AlexJMcIntyre/TildagonAfterlife/PCB/TildagonAfterlife.kicad_sch

## KiCad design PCB/TildagonAfterlife.kicad_sch (2026-07-25)

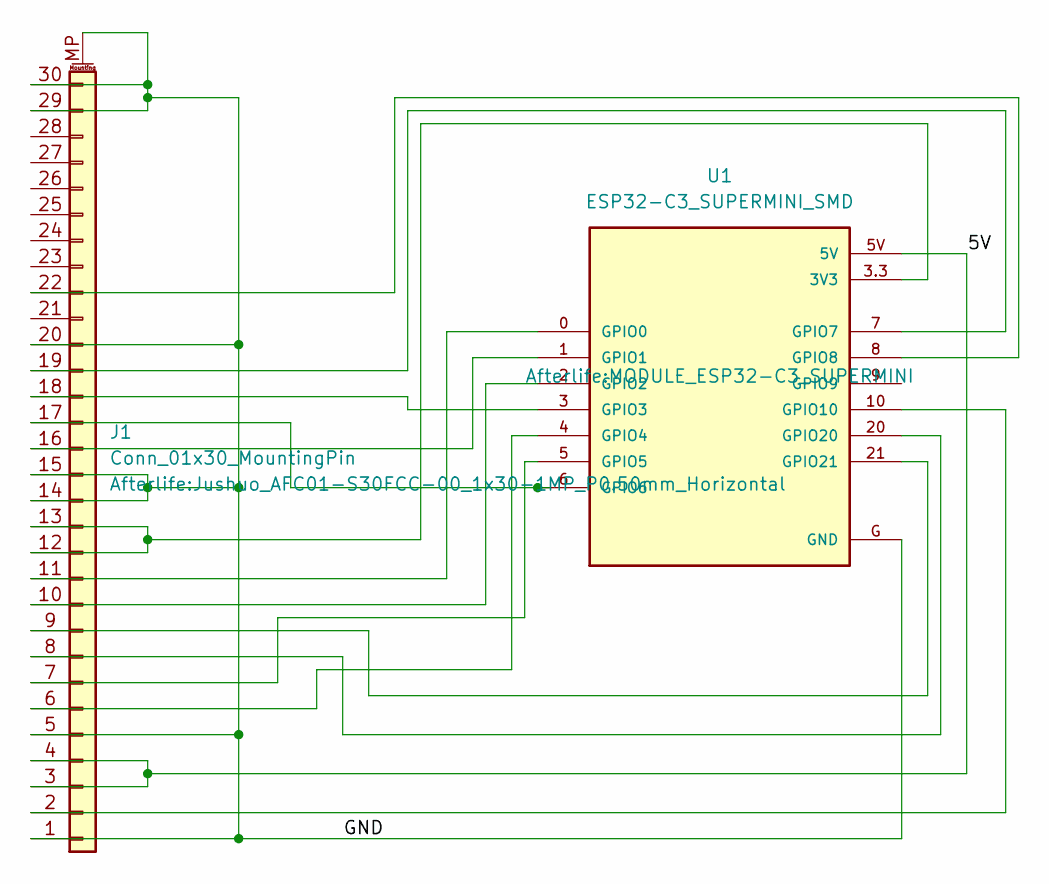
[picture p3: schematic TildagonAfterlife.kicad_sch]

Parts:
J1: Conn_01x30_MountingPin; Jushuo_AFC01-S30FCC-00_1x30-1MP_P0.50mm_Horizontal
U1: ESP32-C3_SUPERMINI_SMD; MODULE_ESP32-C3_SUPERMINI

Connections:
5V: J1.3, J1.4, U1.5V
GND: J1.1, J1.5, J1.14, J1.15, J1.20, J1.29, J1.30, J1.MP (MountPin), U1.G (GND)
unnamed: J1.2, U1.10 (GPIO10)
unnamed: J1.6, U1.4 (GPIO4)
unnamed: J1.7, U1.5 (GPIO5)
unnamed: J1.8, U1.20 (GPIO20)
unnamed: J1.9, U1.21 (GPIO21)
unnamed: J1.10, U1.2 (GPIO2)
unnamed: J1.11, U1.0 (GPIO0)
unnamed: J1.12, J1.13, U1.3.3 (3V3)
unnamed: J1.16, U1.1 (GPIO1)
unnamed: J1.17, U1.6 (GPIO6)
unnamed: J1.18, U1.3 (GPIO3)
unnamed: J1.19, U1.7 (GPIO7)
unnamed: J1.22, U1.8 (GPIO8)
